castellucci5/esp32-robotic-arm-platform/images/elegoo_adapter.png

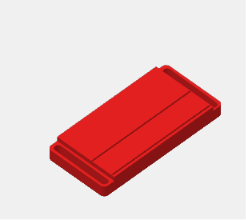
images/elegoo_adapter.png
