castellucci5/esp32-robotic-arm-platform/images/screw_fixing.jpeg

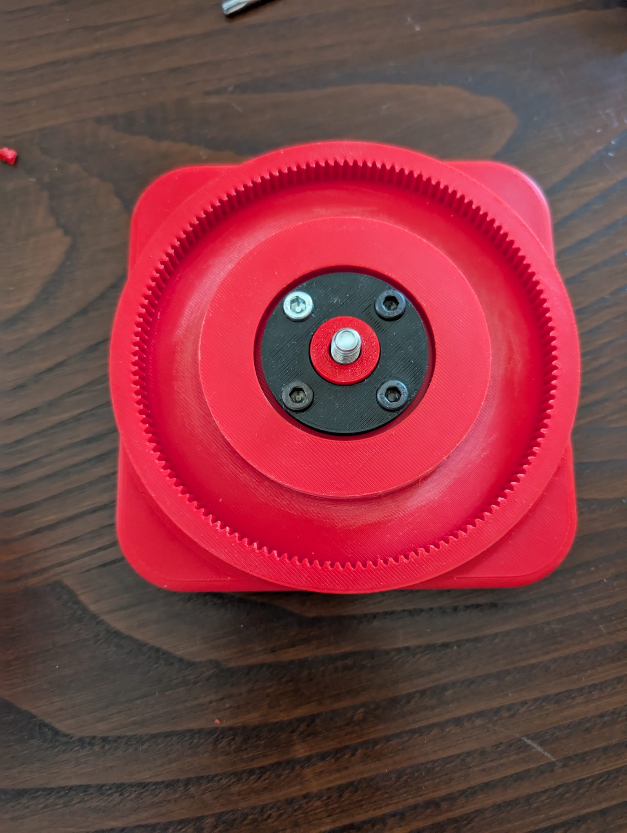
images/screw_fixing.jpeg
