castellucci5/esp32-robotic-arm-platform/images/WhatsApp Image 2026-06-23 at 20.31.28 (24).jpeg

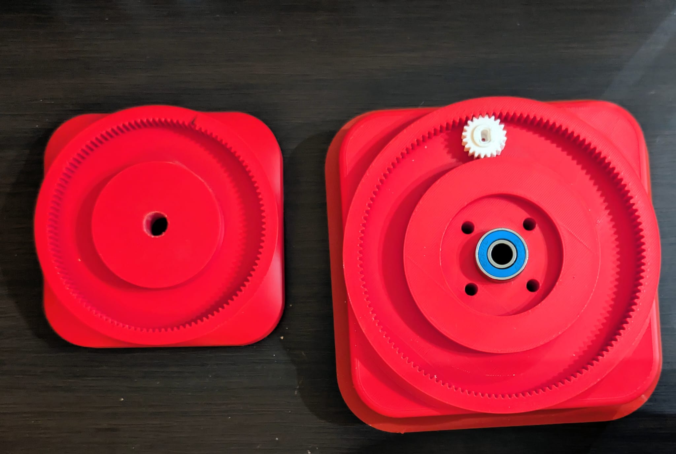
images/WhatsApp Image 2026-06-23 at 20.31.28 (24).jpeg
