castellucci5/esp32-robotic-arm-platform/cad/solidWorks/boccola_cuscinetto.SLDPRT

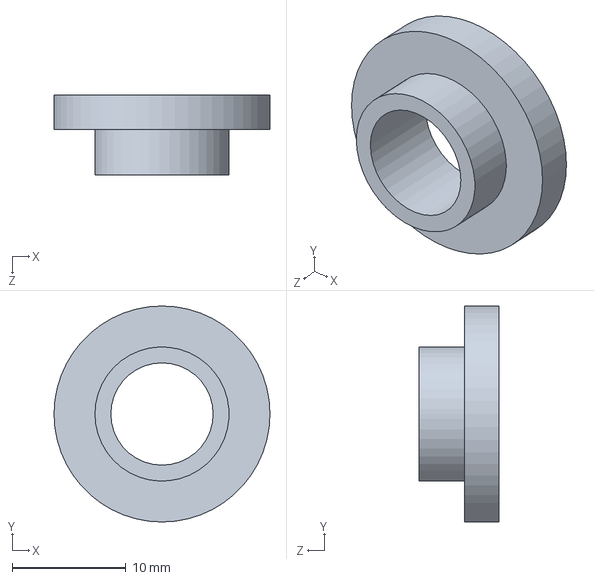
[picture p47: CAD file, 2026-06-24]
cad/solidWorks/boccola_cuscinetto.SLDPRT
19.0 x 19.0 x 7.05 mm
