castellucci5/esp32-robotic-arm-platform/cad/solidWorks/flangia_cuscinetto_base.SLDPRT

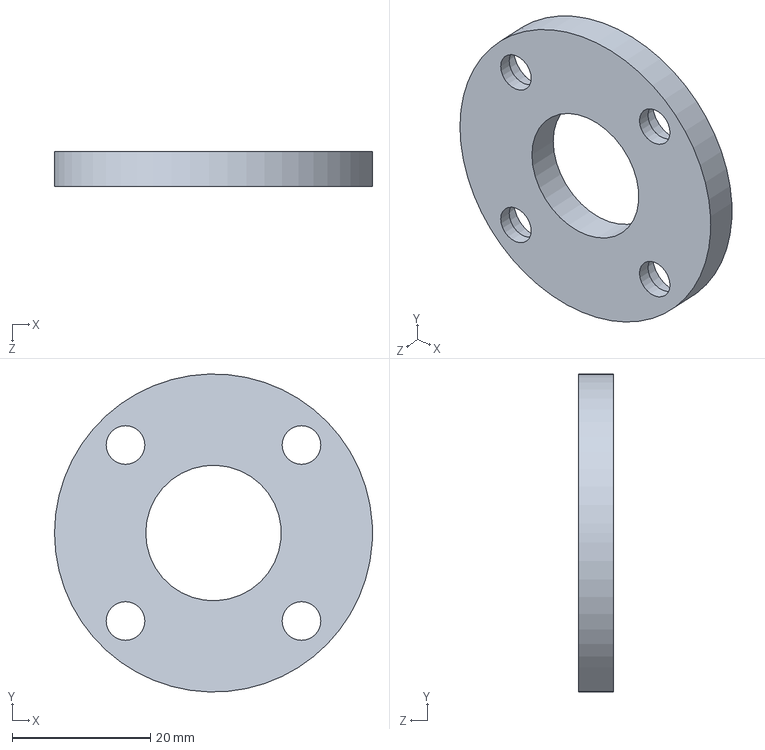
[picture p48: CAD file, 2026-06-24]
cad/solidWorks/flangia_cuscinetto_base.SLDPRT
46.0 x 46.0 x 5.00 mm
