castellucci5/esp32-robotic-arm-platform/cad/solidWorks/base_rotante.SLDPRT

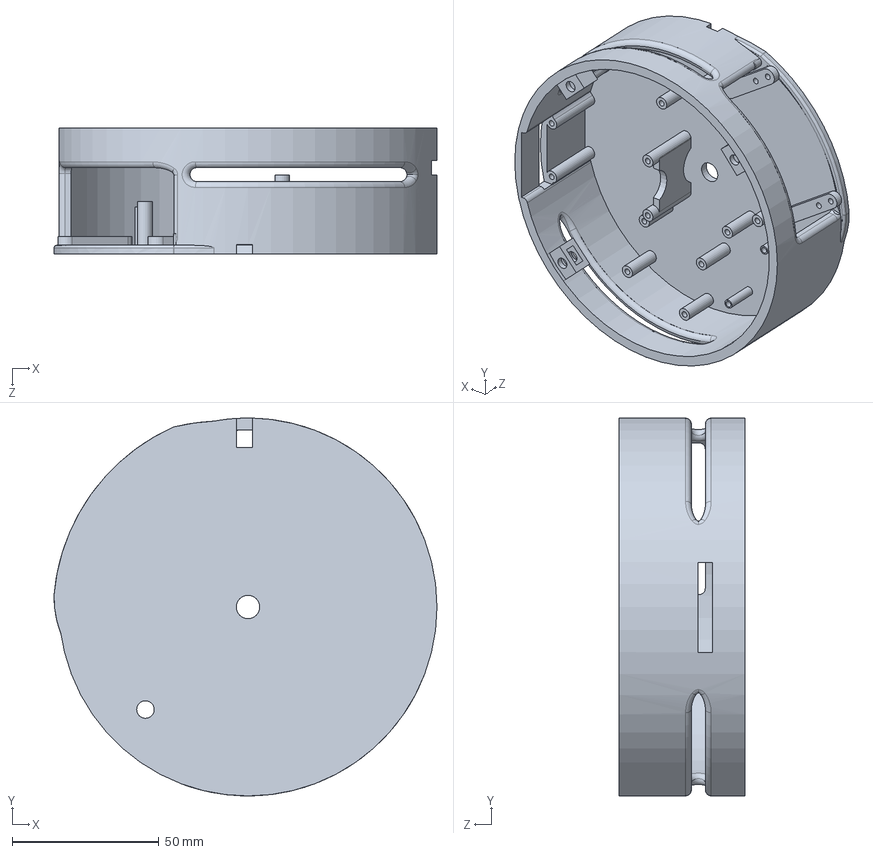
[picture p49: CAD file, 2026-06-24]
cad/solidWorks/base_rotante.SLDPRT
130.7 x 129.0 x 43.0 mm
