castellucci5/esp32-robotic-arm-platform/cad/solidWorks/fissaggio_stepper_motor.SLDPRT

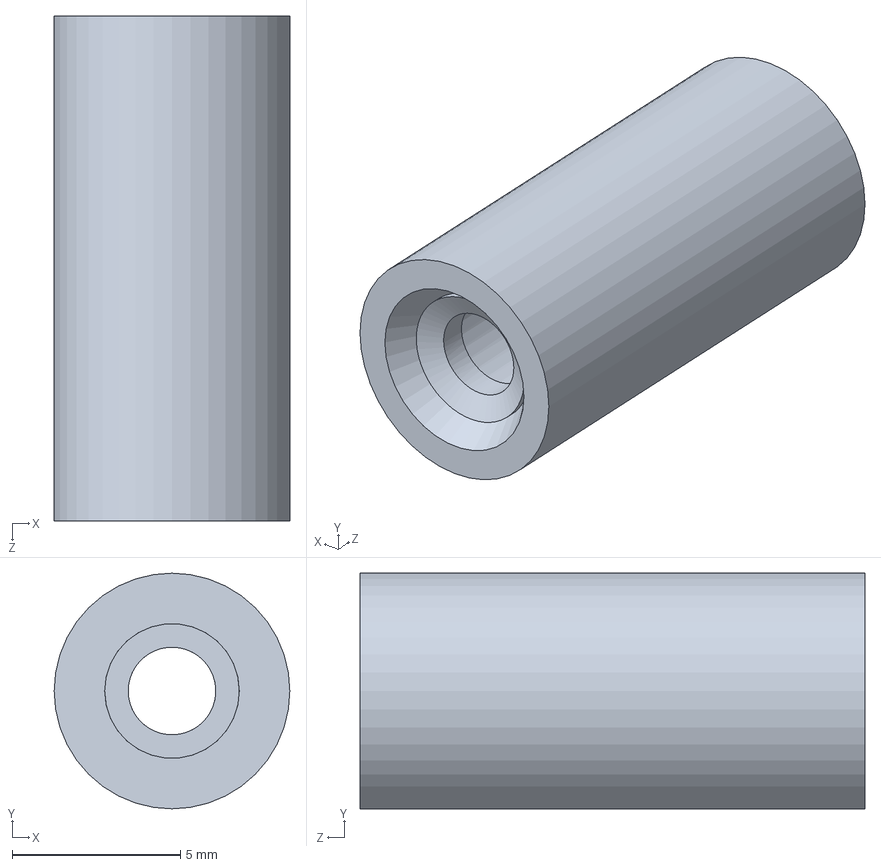
[picture p50: CAD file, 2026-06-24]
cad/solidWorks/fissaggio_stepper_motor.SLDPRT
7.00 x 7.00 x 15.0 mm
